alesgenova/film-memo/src/Action.cpp

#include "Action.h"

#include <WString.h>

#include "common_strings.h"

void Action::asString(uint8_t i, char* s, uint8_t n)
{
  switch (this->type) {
    case ActionType::Edit: {
      strncpy_P(s, PSTR("Edit"), n);
      break;
    }
    case ActionType::Delete: {
      strncpy_P(s, PSTR("Delete"), n);
      break;
    }
    case ActionType::Cancel: {
      strncpy_P(s, PSTR("Cancel"), n);
      break;
    }
    case ActionType::EnableHotShoeShutter: {
      strncpy_P(s, PSTR("Auto shutter"), n);
      break;
    }
    case ActionType::CalibrateHotShoeShutter: {
      strncpy_P(s, PSTR("Calib. shutter"), n);
      break;
    }
    case ActionType::CalibrateMeter: {
      strncpy_P(s, PSTR("Meter const."), n);
      break;
    }
    case ActionType::About: {
      strncpy_P(s, PSTR("About"), n);
      break;
    }
    default: {
      strncpy_P(s, UNKNOWN_STR, n);
      break;
    }
  }

  s[n-1] = '\0';
}
